lastralab/ABISSMAL/Modules/IRBB.py

# Created by PyCharm
# Author: tanismo, gsvidaurre
# Project: Abissmal
# Date: 11/16/2021

# !/usr/bin/env python3

import time
from datetime import datetime
import sys
import csv
import RPi.GPIO as GPIO
from helper import dir_setup
from helper import csv_writer
from helper import box_id
from time import sleep
from subprocess import call
from os import walk
from helper import sms_alert
from helper import get_logger

dir_setup('/home/pi/')

BEAM_PIN_outer = 13
BEAM_PIN_inner = 19
warn = 0
module = 'IRBB'
header = ['chamber_id', 'sensor_id', 'year', 'month', 'day', 'timestamp']
irbb_data = "/home/pi/Data_Abissmal/IRBB/"

logging = get_logger(datetime.today())
logging.info('Started IRBB script')
print('Started IRBB script')

GPIO.setmode(GPIO.BCM)
GPIO.setup(BEAM_PIN_outer, GPIO.IN, pull_up_down=GPIO.PUD_UP)
GPIO.setup(BEAM_PIN_inner, GPIO.IN, pull_up_down=GPIO.PUD_UP)
GPIO.setwarnings(False)


def detect_beam_breaks_callback(BEAM_PIN, sensor_id):
    if not GPIO.input(BEAM_PIN):
        dt = datetime.now()
        logging.info('IRBB activity detected in sensor: ' + sensor_id)
        print('IRBB activity detected in sensor: ' + sensor_id)
        csv_writer(str(box_id), 'IRBB', irbb_data, dt.strftime("%Y_%m_%d"),
                   header, [box_id, sensor_id, dt.strftime("%Y"), dt.strftime("%m"), dt.strftime("%d"), f"{dt:%H:%M:%S.%f}"])
        time.sleep(0.5)
    

GPIO.add_event_detect(BEAM_PIN_outer, GPIO.FALLING,
                      callback=lambda x: detect_beam_breaks_callback(BEAM_PIN_outer, "Outer Beam Breaker"), bouncetime=100)

GPIO.add_event_detect(BEAM_PIN_inner, GPIO.FALLING,
                      callback=lambda x: detect_beam_breaks_callback(BEAM_PIN_inner, "Inner Beam Breaker"), bouncetime=100)


try:
    while True:
        pass
except KeyboardInterrupt:
    logging.info('exiting IRBB')
    print('exiting IRBB')
    GPIO.cleanup()
except Exception as E:
    logging.error('IRBB error: ' + str(E))
    print('IRBB error: ' + str(E))
    sms_alert('IRBB', 'Error: ' + str(E))
finally:
    GPIO.cleanup()
